woochang0110/Car_Info_Transmission_Using_IoT/esp32_tp_library/iso-tp-esp32.cpp

#include "iso-tp-esp32.h"

IsoTp::IsoTp(ESP32_CAN* bus)
{
  _bus = bus;
}

void IsoTp::print_buffer(INT32U id, INT8U *buffer, uint16_t len)
{
  uint16_t i=0;

  Serial.print(F("Buffer: "));
  Serial.print(id,HEX); Serial.print(F(" ["));
  Serial.print(len); Serial.print(F("] "));
  for(i=0;i<len;i++)
  {
    if(buffer[i] < 0x10) Serial.print(F("0"));
    Serial.print(buffer[i],HEX);
    Serial.print(F(" "));
  }
  Serial.println();
}

INT8U IsoTp::can_send(INT32U id, INT8U len, INT8U *data)
{
#ifdef ISO_TP_DEBUG
  Serial.println(F("Send CAN RAW Data:"));
  print_buffer(id, data, len);
#endif
  return _bus->sendMsgBuf(id, 0, len, data);
}

INT8U IsoTp::can_receive(void)
{
  if (_bus->checkReceive() == CAN_MSGAVAIL)            // If pin is low, read receive buffer
  {
     memset(rxBuffer,0,sizeof(rxBuffer));       // Cleanup Buffer
     _bus->readMsgBuf(&rxId, &rxLen, rxBuffer); // Read data: buf = data byte(s)
#ifdef ISO_TP_DEBUG
     Serial.println(F("Received CAN RAW Data:"));
     print_buffer(rxId, rxBuffer, rxLen);
#endif
    return true;
  }
  else return false;
}

INT8U IsoTp::send_fc(struct Message_t *msg)
{
  INT8U TxBuf[8]={0x00, 0x00, 0x00, 0x00, 0x00, 0x00, 0x00, 0x00};
  // FC message high nibble = 0x3 , low nibble = FC Status
  TxBuf[0]=(N_PCI_FC | msg->fc_status);
  TxBuf[1]=msg->blocksize;
  /* fix wrong separation time values according spec */
  if ((msg->min_sep_time > 0x7F) && ((msg->min_sep_time < 0xF1) 
      || (msg->min_sep_time > 0xF9))) msg->min_sep_time = 0x7F;
  TxBuf[2]=msg->min_sep_time;
  return can_send(msg->tx_id,8,TxBuf);
}

INT8U IsoTp::send_sf(struct Message_t *msg) //Send SF Message
{
  INT8U TxBuf[8]={0x00, 0x00, 0x00, 0x00, 0x00, 0x00, 0x00, 0x00};
  // SF message high nibble = 0x0 , low nibble = Length
  TxBuf[0]=(N_PCI_SF | msg->len);
  memcpy(TxBuf+1,msg->Buffer,msg->len);
//  return can_send(msg->tx_id,msg->len+1,TxBuf);// Add PCI length
  return can_send(msg->tx_id,8,TxBuf);// Always send full frame
}

INT8U IsoTp::send_ff(struct Message_t *msg) // Send FF
{
  INT8U TxBuf[8]={0x00, 0x00, 0x00, 0x00, 0x00, 0x00, 0x00, 0x00};
  msg->seq_id=1;

  TxBuf[0]=(N_PCI_FF | ((msg->len&0x0F00) >> 8));
  TxBuf[1]=(msg->len&0x00FF);
  memcpy(TxBuf+2,msg->Buffer,6);             // Skip 2 Bytes PCI
  return can_send(msg->tx_id,8,TxBuf);       // First Frame has full length
}

INT8U IsoTp::send_cf(struct Message_t *msg) // Send SF Message
{
  INT8U TxBuf[8]={0x00, 0x00, 0x00, 0x00, 0x00, 0x00, 0x00, 0x00};
  uint16_t len=7;
		 
  TxBuf[0]=(N_PCI_CF | (msg->seq_id & 0x0F));
  if(msg->len>7) len=7; else len=msg->len;
  memcpy(TxBuf+1,msg->Buffer,len);         // Skip 1 Byte PCI
  //return can_send(msg->tx_id,len+1,TxBuf); // Last frame is probably shorter
                                           // than 8 -> Signals last CF Frame
  return can_send(msg->tx_id,8,TxBuf);     // Last frame is probably shorter
                                           // than 8, pad with 00 
}

void IsoTp::fc_delay(INT8U sep_time)
{
  if(sep_time < 0x80)
    delay(sep_time);
  else
    delayMicroseconds((sep_time-0xF0)*100);
}

INT8U IsoTp::rcv_sf(struct Message_t* msg)
{
  /* get the SF_DL from the N_PCI byte */
  msg->len = rxBuffer[0] & 0x0F;
  /* copy the received data bytes */
  memcpy(msg->Buffer,rxBuffer+1,msg->len); // Skip PCI, SF uses len bytes
  msg->tp_state=ISOTP_FINISHED;

  return 0;
}

INT8U IsoTp::rcv_ff(struct Message_t* msg)
{
  msg->seq_id=1;

  /* get the FF_DL */
  msg->len = (rxBuffer[0] & 0x0F) << 8;
  msg->len += rxBuffer[1];
  rest=msg->len;

  /* copy the first received data bytes */
  memcpy(msg->Buffer,rxBuffer+2,6); // Skip 2 bytes PCI, FF must have 6 bytes! 
  rest-=6; // Restlength

  msg->tp_state = ISOTP_WAIT_DATA;

#ifdef ISO_TP_DEBUG
  Serial.print(F("First frame received with message length: "));
  Serial.println(rest);
  Serial.println(F("Send flow controll."));
  Serial.print(F("ISO-TP state: ")); Serial.println(msg->tp_state);
#endif

  /* send our first FC frame with Target Address*/
  struct Message_t fc;
  fc.tx_id=msg->tx_id;
  fc.fc_status=ISOTP_FC_CTS;
  fc.blocksize=0;
  fc.min_sep_time=0;
  return send_fc(&fc);
}

INT8U IsoTp::rcv_cf(struct Message_t* msg)
{
  //Handle Timeout
  //If no Frame within 250ms change State to ISOTP_IDLE
  INT32U delta=millis()-wait_cf;

  if((delta >= TIMEOUT_FC) && msg->seq_id>1)
  {
#ifdef ISO_TP_DEBUG
    Serial.println(F("CF frame timeout during receive wait_cf="));
    Serial.print(wait_cf); Serial.print(F(" delta="));
    Serial.println(delta);
#endif
    msg->tp_state = ISOTP_IDLE;
    return 1;
  }
  wait_cf=millis();

#ifdef ISO_TP_DEBUG
  Serial.print(F("ISO-TP state: ")); Serial.println(msg->tp_state);
  Serial.print(F("CF received with message rest length: "));
  Serial.println(rest);
#endif

  if (msg->tp_state != ISOTP_WAIT_DATA) return 0;

  if ((rxBuffer[0] & 0x0F) != msg->seq_id)
  {
#ifdef ISO_TP_DEBUG
    Serial.print(F("Got sequence ID: ")); Serial.print(rxBuffer[0] & 0x0F);
    Serial.print(F(" Expected: ")); Serial.println(msg->seq_id);
#endif
    msg->tp_state = ISOTP_IDLE;
    msg->seq_id = 1;
    return 1;
  }

  if(rest<=7) // Last Frame
  {
    memcpy(msg->Buffer+6+7*(msg->seq_id-1),rxBuffer+1,rest);// 6 Bytes in FF +7
    msg->tp_state=ISOTP_FINISHED;                           // per CF skip PCI
#ifdef ISO_TP_DEBUG
    Serial.print(F("Last CF received with seq. ID: "));
    Serial.println(msg->seq_id);
#endif
  }
  else
  {
#ifdef ISO_TP_DEBUG
    Serial.print(F("CF received with seq. ID: "));
    Serial.println(msg->seq_id);
#endif
    memcpy(msg->Buffer+6+7*(msg->seq_id-1),rxBuffer+1,7); // 6 Bytes in FF +7 
                                                          // per CF
    rest-=7; // Got another 7 Bytes of Data;
  }

  msg->seq_id++;
  msg->seq_id %= 16; // Wrap around

  return 0;
}

INT8U IsoTp::rcv_fc(struct Message_t* msg)
{
  INT8U retval=0;

  if (msg->tp_state != ISOTP_WAIT_FC && msg->tp_state != ISOTP_WAIT_FIRST_FC)
    return 0;

  /* get communication parameters only from the first FC frame */
  if (msg->tp_state == ISOTP_WAIT_FIRST_FC)
  {
    msg->blocksize = rxBuffer[1];
    msg->min_sep_time = rxBuffer[2];

    /* fix wrong separation time values according spec */
    if ((msg->min_sep_time > 0x7F) && ((msg->min_sep_time < 0xF1) 
	|| (msg->min_sep_time > 0xF9))) msg->min_sep_time = 0x7F;
  }

#ifdef ISO_TP_DEBUG
  Serial.print(F("FC frame: FS "));
  Serial.print(rxBuffer[0]&0x0F);
  Serial.print(F(", Blocksize "));
  Serial.print(msg->blocksize);
  Serial.print(F(", Min. separation Time "));
  Serial.println(msg->min_sep_time);
#endif
  
  switch (rxBuffer[0] & 0x0F)
  {
    case ISOTP_FC_CTS:
                         msg->tp_state = ISOTP_SEND_CF;
                         break;
    case ISOTP_FC_WT:
                         fc_wait_frames++;
			 if(fc_wait_frames >= MAX_FCWAIT_FRAME)
                         {
#ifdef ISO_TP_DEBUG
                           Serial.println(F("FC wait frames exceeded."));
#endif
                           fc_wait_frames=0;
                           msg->tp_state = ISOTP_IDLE;
                           retval=1;
                         }
#ifdef ISO_TP_DEBUG
                         Serial.println(F("Start waiting for next FC"));
#endif
                         break;
    case ISOTP_FC_OVFLW:
#ifdef ISO_TP_DEBUG
                         Serial.println(F("Overflow in receiver side"));
#endif
    default:
                         msg->tp_state = ISOTP_IDLE;
                         retval=1;
  }
  return retval;
}

INT8U IsoTp::send(Message_t* msg)
{
  INT8U bs=false;
  INT32U delta=0;
  INT8U retval=0;

  msg->tp_state=ISOTP_SEND;

  while(msg->tp_state!=ISOTP_IDLE && msg->tp_state!=ISOTP_ERROR)
  {
    bs=false;

#ifdef ISO_TP_DEBUG
    Serial.print(F("ISO-TP State: ")); Serial.println(msg->tp_state);
    Serial.print(F("Length      : ")); Serial.println(msg->len);
#endif

    switch(msg->tp_state)
    {
      case ISOTP_IDLE         :  break;
      case ISOTP_SEND         :
                                 if(msg->len<=7)
                                 {
#ifdef ISO_TP_DEBUG
                                   Serial.println(F("Send SF"));
#endif
                                   retval=send_sf(msg);
                                   msg->tp_state=ISOTP_IDLE;
                                 }
                                 else
                                 {
#ifdef ISO_TP_DEBUG
                                   Serial.println(F("Send FF"));
#endif
                                   if(!(retval=send_ff(msg))) // FF complete
                                   {
                                     msg->Buffer+=6;
                                     msg->len-=6;
                                     msg->tp_state=ISOTP_WAIT_FIRST_FC;
                                     fc_wait_frames=0;
                                     wait_fc=millis();
                                   }
                                 }
                                 break;
      case ISOTP_WAIT_FIRST_FC:
#ifdef ISO_TP_DEBUG
                                 Serial.println(F("Wait first FC"));
#endif
                                 delta=millis()-wait_fc;
                                 if(delta >= TIMEOUT_FC)
                                 {
#ifdef ISO_TP_DEBUG
                                   Serial.print(F("FC timeout during receive"));
                                   Serial.print(F(" wait_fc="));
                                   Serial.print(wait_fc);
                                   Serial.print(F(" delta="));
                                   Serial.println(delta);
#endif
                                   msg->tp_state = ISOTP_IDLE;
				   retval=1;
                                 }
                                 break;
      case ISOTP_WAIT_FC      :
#ifdef ISO_TP_DEBUG
                                 Serial.println(F("Wait FC"));
#endif
                                 break;
      case ISOTP_SEND_CF      : 
#ifdef ISO_TP_DEBUG
                                 Serial.println(F("Send CF"));
#endif
                                 while(msg->len>7 & !bs) 
                                 {
                                   fc_delay(msg->min_sep_time);
                                   if(!(retval=send_cf(msg)))
                                   {
#ifdef ISO_TP_DEBUG
                                     Serial.print(F("Send Seq "));
                                     Serial.println(msg->seq_id);
#endif
                                     if(msg->blocksize > 0)
                                     {
#ifdef ISO_TP_DEBUG
                                       Serial.print(F("Blocksize trigger "));
                                       Serial.print(msg->seq_id % 
                                                    msg->blocksize);
#endif
                                       if(!(msg->seq_id % msg->blocksize))
                                       {
                                         bs=true;
                                         msg->tp_state=ISOTP_WAIT_FC;
#ifdef ISO_TP_DEBUG
                                         Serial.println(F(" yes"));
#endif
                                       } 
#ifdef ISO_TP_DEBUG
                                       else Serial.println(F(" no"));
#endif
                                     }
                                     msg->seq_id++;
                                     msg->seq_id %= 16;
                                     msg->Buffer+=7;
                                     msg->len-=7;
#ifdef ISO_TP_DEBUG
                                     Serial.print(F("Length      : "));
                                     Serial.println(msg->len);
#endif
                                   }
                                 }
                                 if(!bs)
                                 {
                                   fc_delay(msg->min_sep_time);
#ifdef ISO_TP_DEBUG
                                   Serial.print(F("Send last Seq "));
                                   Serial.println(msg->seq_id);
#endif
                                   retval=send_cf(msg);
                                   msg->tp_state=ISOTP_IDLE;
                                 }
                                 break;
      default                 :  break;
    }

    
    if(msg->tp_state==ISOTP_WAIT_FIRST_FC || 
       msg->tp_state==ISOTP_WAIT_FC)
    {
      if(can_receive())
      {
#ifdef ISO_TP_DEBUG
        Serial.println(F("Send branch:"));
#endif
        if(rxId==msg->rx_id)
        {
          retval=rcv_fc(msg);
          memset(rxBuffer,0,sizeof(rxBuffer));
#ifdef ISO_TP_DEBUG
          Serial.println(F("rxId OK!"));
#endif
        }
      }
    }
  }

  return retval;
}

INT8U IsoTp::receive(Message_t* msg)
{
  INT8U n_pci_type=0;
  INT32U delta=0;

  wait_session=millis();
#ifdef ISO_TP_DEBUG
  Serial.println(F("Start receive..."));
#endif
  msg->tp_state=ISOTP_IDLE;

  while(msg->tp_state!=ISOTP_FINISHED && msg->tp_state!=ISOTP_ERROR)
  {
    delta=millis()-wait_session;
    if(delta >= TIMEOUT_SESSION)
    {
#ifdef ISO_TP_DEBUG
      Serial.print(F("ISO-TP Session timeout wait_session="));
      Serial.print(wait_session); Serial.print(F(" delta="));
      Serial.println(delta);
#endif
      return 1;
    }

    if(can_receive())
    {
      if(rxId==msg->rx_id)
      {
#ifdef ISO_TP_DEBUG
        Serial.println(F("rxId OK!"));
#endif
        n_pci_type=rxBuffer[0] & 0xF0;

        switch (n_pci_type)
        {
          case N_PCI_FC:
#ifdef ISO_TP_DEBUG
                      Serial.println(F("FC"));
#endif
                      /* tx path: fc frame */
                      rcv_fc(msg);
                      break;

          case N_PCI_SF:
#ifdef ISO_TP_DEBUG
                      Serial.println(F("SF"));
#endif
                      /* rx path: single frame */
                      rcv_sf(msg);
//		      msg->tp_state=ISOTP_FINISHED;
                      break;

          case N_PCI_FF:
#ifdef ISO_TP_DEBUG
                      Serial.println(F("FF"));
#endif
                      /* rx path: first frame */
                      rcv_ff(msg);
//		      msg->tp_state=ISOTP_WAIT_DATA;
                      break;
                      break;

          case N_PCI_CF:
#ifdef ISO_TP_DEBUG
                      Serial.println(F("CF"));
#endif
                      /* rx path: consecutive frame */
                      rcv_cf(msg);
                      break;
        }
        memset(rxBuffer,0,sizeof(rxBuffer));
      }
    }
  }
#ifdef ISO_TP_DEBUG
  Serial.println(F("ISO-TP message received:"));
  print_buffer(msg->rx_id, msg->Buffer, msg->len);
#endif

  return 0;
}
