woochang0110/Car_Info_Transmission_Using_IoT/esp32_can_library/examples/CAN_receive/CAN_receive.ino

// CAN Receive Example
//

#include <esp32_can.h>

long unsigned int rxId;
unsigned char len = 0;
unsigned char rxBuf[8];

ESP32_CAN CAN0;

void setup()
{
  Serial.begin(115200);
  
  // Initialize ESP32 CAN with a baudrate of 500kb/s and tx pin 16, rx pin 17.
  if(CAN0.begin(16,17,CAN_500KBPS) == CAN_OK){
	Serial.println("ESP32 CAN Initialized Successfully!");
	Serial.println("ESP32 CAN Library Receive Example...");	
  } else {
	Serial.println("Error Initializing ESP32 CAN..."); 
	return;	
  }
}

void loop()
{
    if(CAN0.checkReceive() == CAN_MSGAVAIL) 
    {
      CAN0.readMsgBuf(&rxId, &len, rxBuf);              // Read data: len = data length, buf = data byte(s)

      Serial.print("ID: ");                     // Print the message ID.
      Serial.print(rxId, HEX);

      
      Serial.print(" len: ");                     // Print the message length.
      Serial.print(len);

      Serial.print("  Data: ");
      for(int i = 0; i<len; i++)                // Print each byte of the data.
      {
        if(rxBuf[i] < 0x10)                     // If data byte is less than 0x10, add a leading zero.
        {
          Serial.print("0");
        }
        Serial.print(rxBuf[i], HEX);
        Serial.print(" ");
      }

      Serial.println();
    }
}

/*********************************************************************************************************
  END FILE
*********************************************************************************************************/
